Veziik/X95-TeleStock/CAM Job Files/v3 and earlier/jobs/SanityCheck/baseimage_t.png

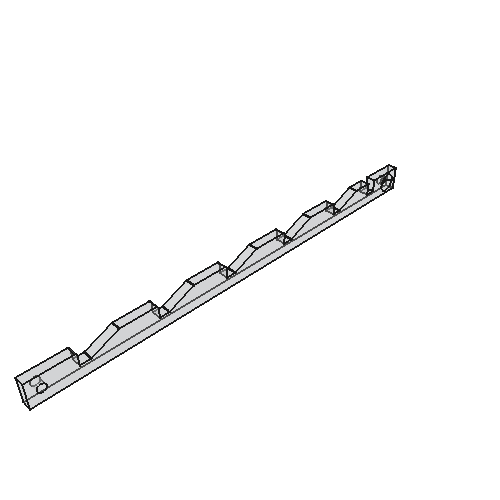
CAM Job Files/v3 and earlier/jobs/SanityCheck/baseimage_t.png
