Veziik/X95-TeleStock/CAM Job Files/v3 and earlier/jobs/SanityCheck/stockImage.png

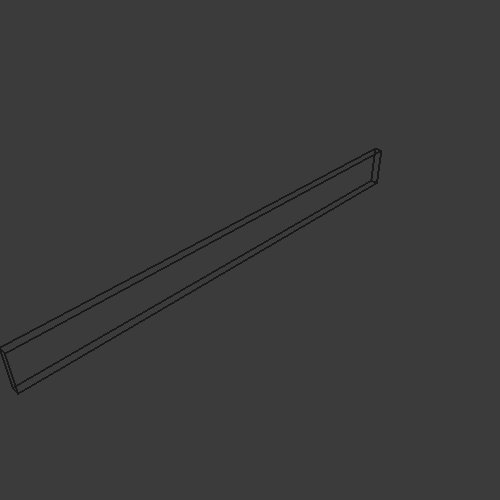
CAM Job Files/v3 and earlier/jobs/SanityCheck/stockImage.png
