Veziik/X95-TeleStock/Ender 5 Calibrated Files/ClevisPinSlotCover.stl

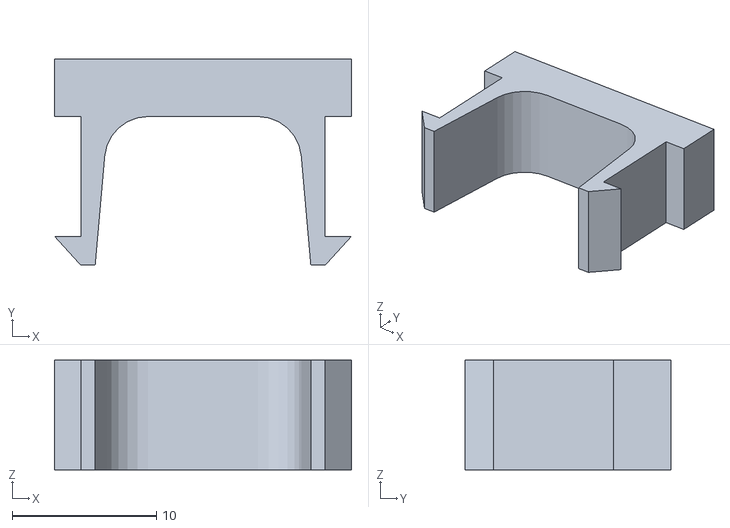
[picture p19: CAD file, 2026-01-05]
Ender 5 Calibrated Files/ClevisPinSlotCover.stl
20.6 x 14.3 x 7.60
