Veziik/X95-TeleStock/Modeling Files/Jigs and Spacers/step files/BarJig-BarSpacer-3-16inBar.step

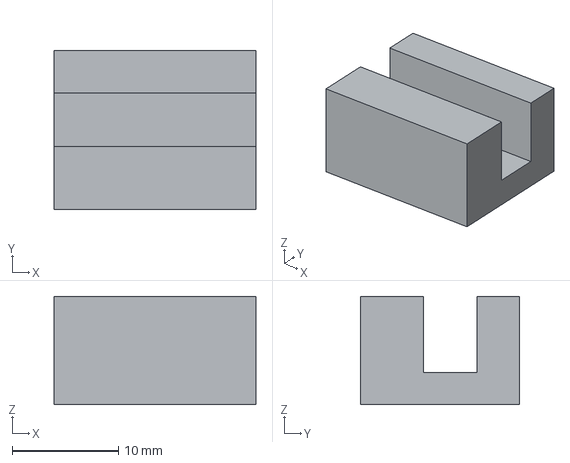
[picture p20: CAD file, 2026-07-19]
Modeling Files/Jigs and Spacers/step files/BarJig-BarSpacer-3-16inBar.step
19.0 x 15.0 x 10.2 mm
