Veziik/X95-TeleStock/X95TelescopingStock.FCStd

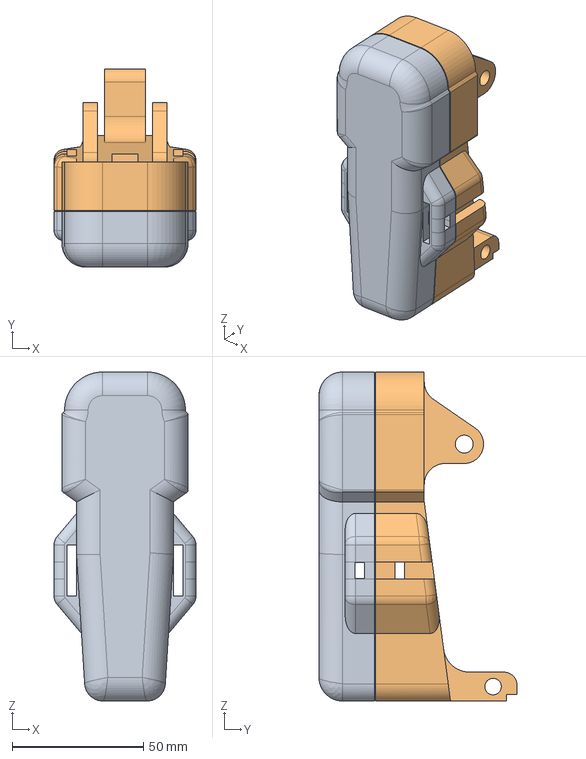
[picture p21: CAD file, 2024-03-01]
X95TelescopingStock.FCStd
54.2 x 75.6 x 125.5 mm
TelescopingPad
LockingBody
