Veziik/X95-TeleStock/Content Files/PaperworkSlotCover.step

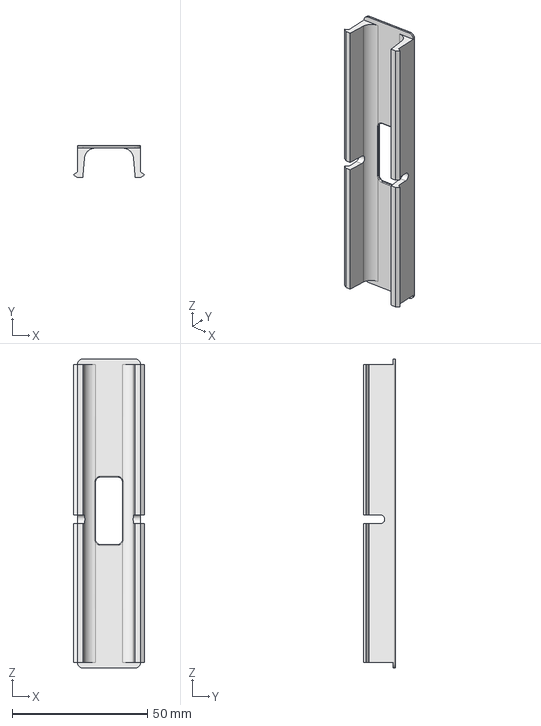
[picture p22: CAD file, 2026-07-30]
Content Files/PaperworkSlotCover.step
26.4 x 11.9 x 114.4 mm
