Veziik/X95-TeleStock/Content Files/WIP - Original Config - Updated Butt Texture - Rack UnEdited/TopPinArmPin.step

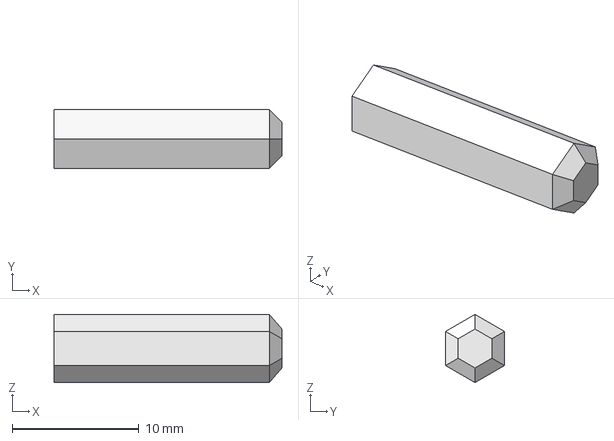
[picture p23: CAD file, 2026-07-19]
Content Files/WIP - Original Config - Updated Butt Texture - Rack UnEdited/TopPinArmPin.step
18.0 x 4.66 x 5.38 mm
