Veziik/X95-TeleStock/Content Files/WIP2 - RackProfileMovedRearwards/LockingPin.step

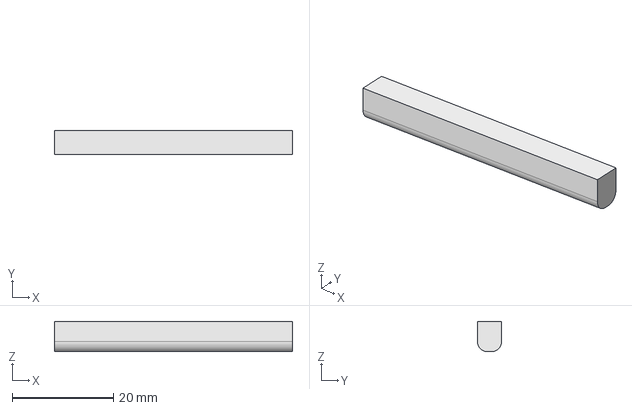
[picture p24: CAD file, 2026-07-19]
Content Files/WIP2 - RackProfileMovedRearwards/LockingPin.step
47.0 x 4.76 x 6.00 mm
