Veziik/X95-TeleStock/Ender 5 Calibrated Files/LockingBody.stl

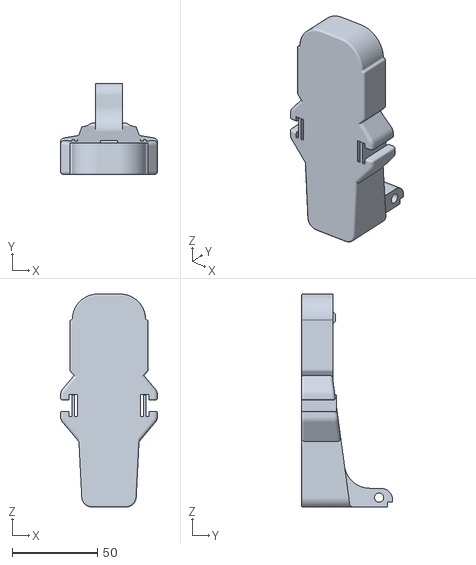
[picture p25: CAD file, 2026-01-05]
Ender 5 Calibrated Files/LockingBody.stl
56.9 x 53.6 x 125.0
