Veziik/X95-TeleStock/CAM Job Files/v3 and earlier/CAMAluminumLEftBar.FCStd

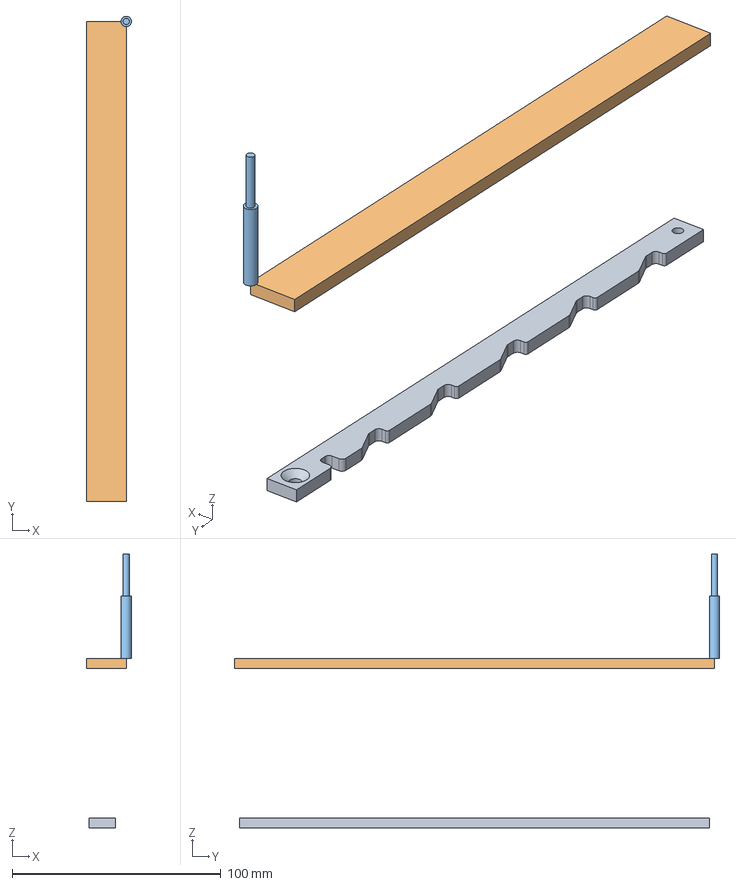
[picture p26: CAD file, 2026-07-19]
CAM Job Files/v3 and earlier/CAMAluminumLEftBar.FCStd
21.6 x 232.5 x 131.2 mm
Model-TelescopingBarArm-Left
Stock001
Endmill
