Veziik/X95-TeleStock/Content Files/TelescopingPad.step

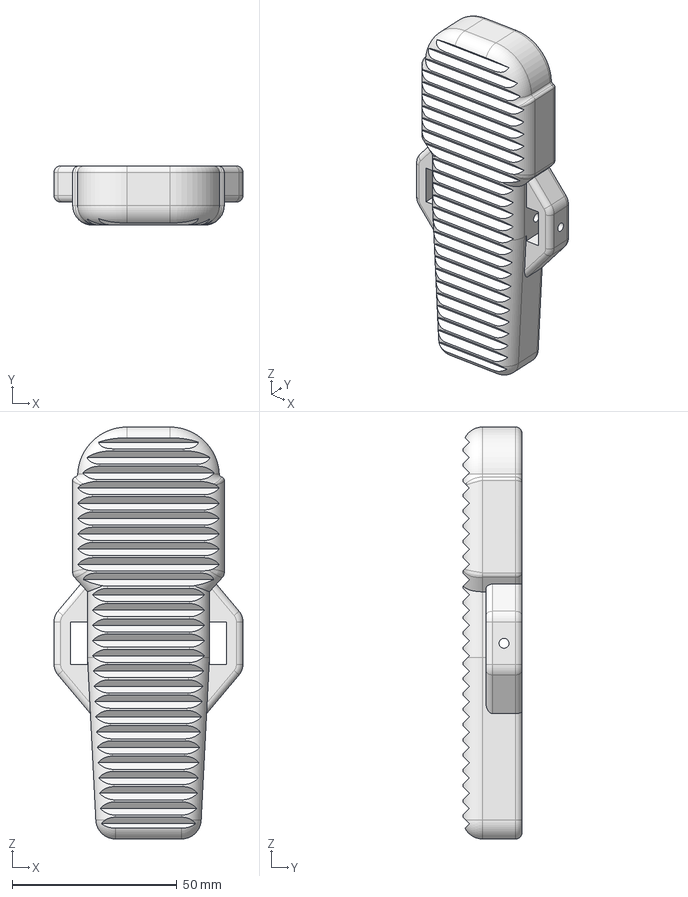
[picture p27: CAD file, 2026-07-23]
Content Files/TelescopingPad.step
57.3 x 18.0 x 125.0 mm
