Veziik/X95-TeleStock/Ender 5 Calibrated Files/PaperworkSlotLid.stl

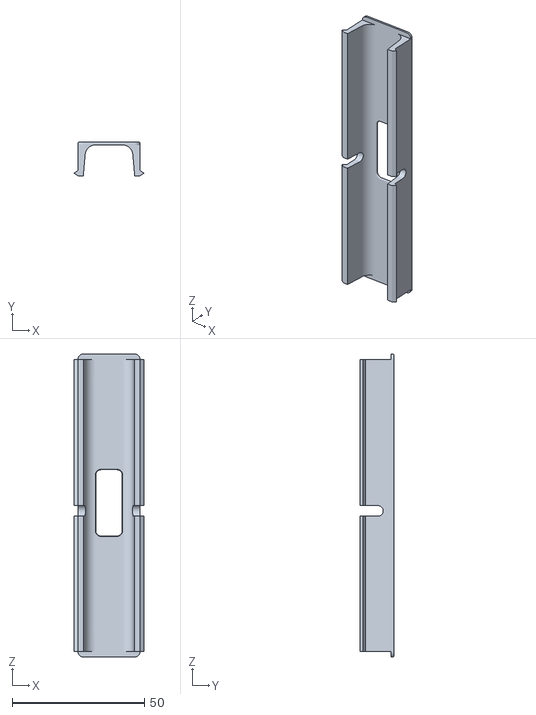
[picture p28: CAD file, 2026-01-05]
Ender 5 Calibrated Files/PaperworkSlotLid.stl
26.4 x 12.7 x 114.4
