Veziik/X95-TeleStock/Modeling Files/Jigs and Spacers/step files/BarSupport.step

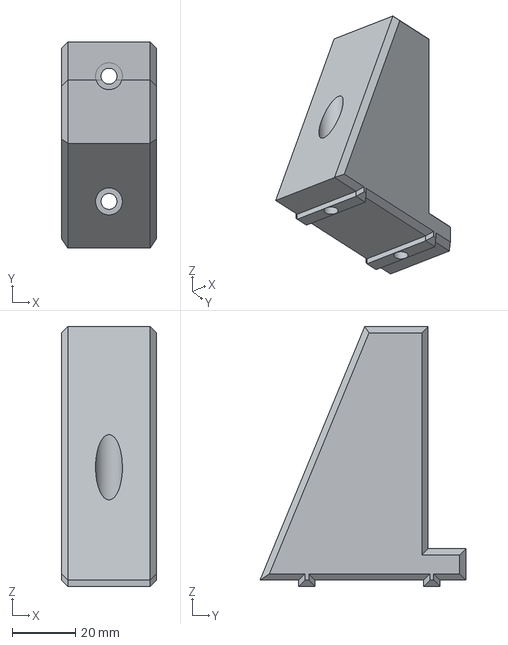
[picture p29: CAD file, 2026-07-19]
Modeling Files/Jigs and Spacers/step files/BarSupport.step
30.0 x 65.0 x 82.0 mm
