Veziik/X95-TeleStock/Modeling Files/X95SolidStock.FCStd

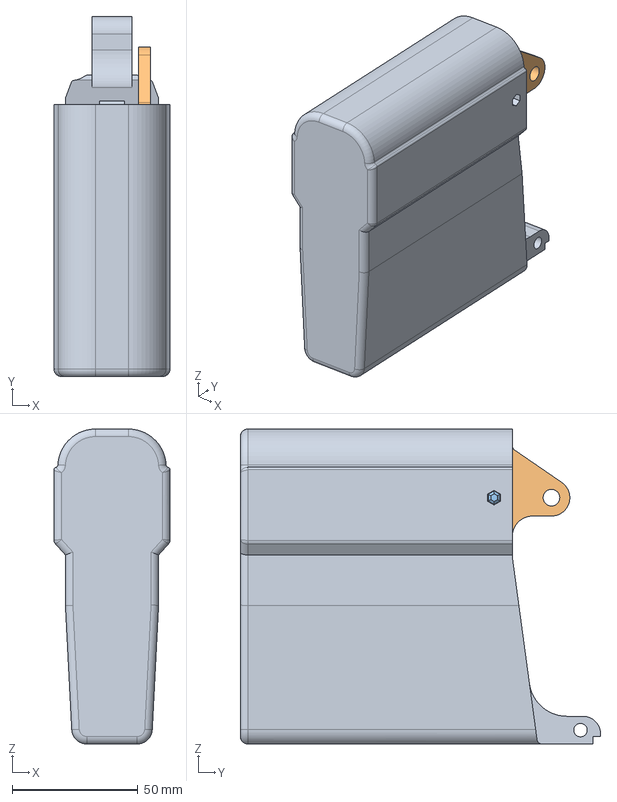
[picture p30: CAD file, 2026-07-19]
Modeling Files/X95SolidStock.FCStd
46.0 x 143.0 x 125.0 mm
SolidBody
MetalPinArm
TopPinArmPin
