Veziik/X95-TeleStock/CAM Job Files/v3 and earlier/CAMAluminumRightBar.FCStd

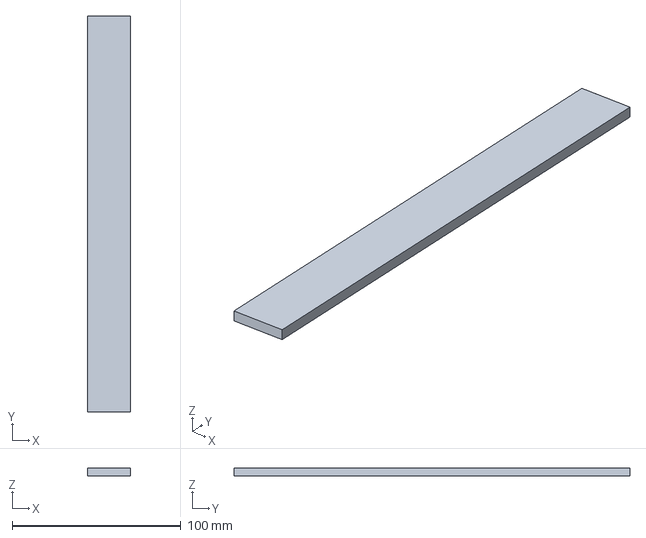
[picture p31: CAD file, 2026-07-19]
CAM Job Files/v3 and earlier/CAMAluminumRightBar.FCStd
25.4 x 235.0 x 4.76 mm
