Veziik/X95-TeleStock/Content Files/TopPinArmPin.step

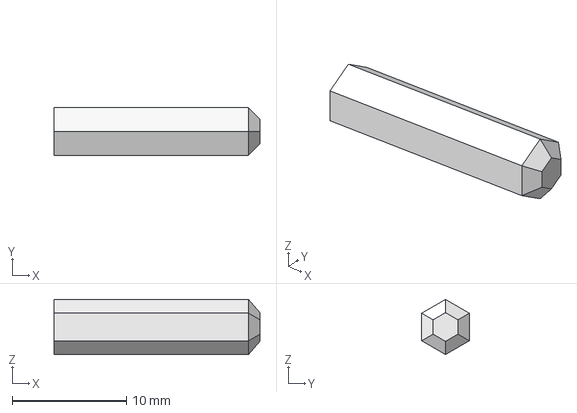
[picture p32: CAD file, 2026-07-23]
Content Files/TopPinArmPin.step
18.0 x 4.17 x 4.82 mm
