Veziik/X95-TeleStock/Ender 5 Calibrated Files/LockingBody for MetalPinArms.stl

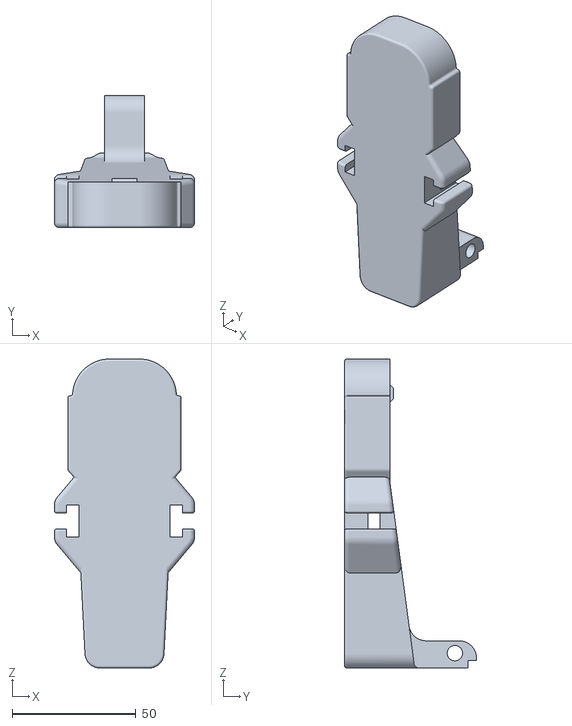
[picture p33: CAD file, 2024-08-24]
Ender 5 Calibrated Files/LockingBody for MetalPinArms.stl
56.7 x 53.4 x 125.0
