Veziik/X95-TeleStock/Modeling Files/Jigs and Spacers/step files/BarJig-BarSpacer-3-16inBarLong.step

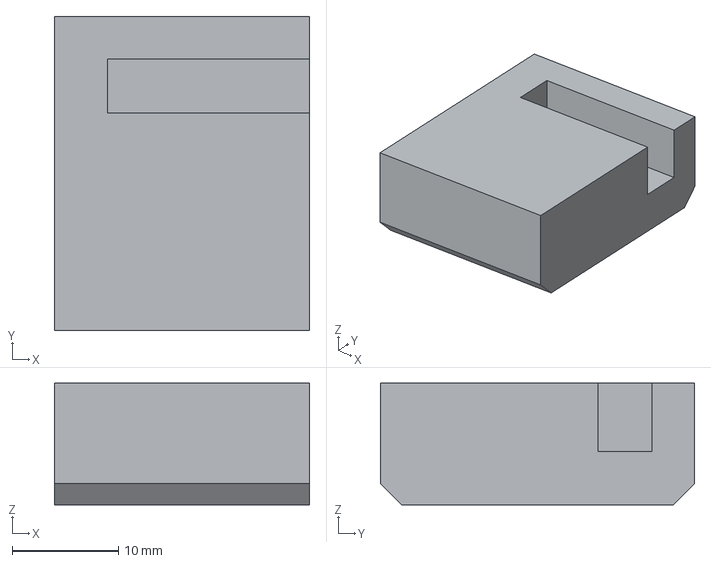
[picture p34: CAD file, 2026-07-19]
Modeling Files/Jigs and Spacers/step files/BarJig-BarSpacer-3-16inBarLong.step
24.0 x 29.5 x 11.4 mm
