Veziik/X95-TeleStock/Modeling Files/X95TelescopingStock-MetalPinoleArmsBetterModeling.FCStd

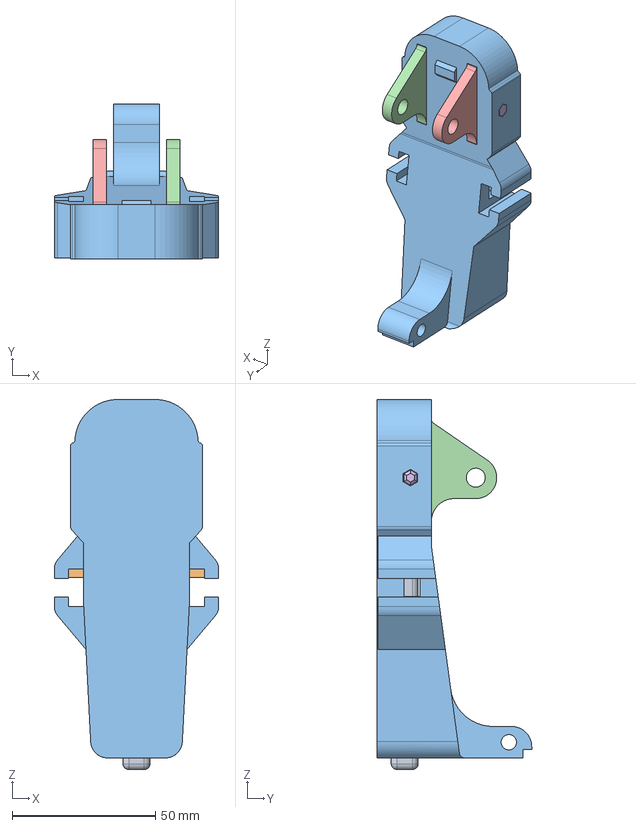
[picture p35: CAD file, 2026-07-19]
Modeling Files/X95TelescopingStock-MetalPinoleArmsBetterModeling.FCStd
57.3 x 53.9 x 129.0 mm
LockingButton
LockingPin
LockingBody
MetalPinArmMainBody
MetalPinArmMainBody (Mirror #3)
TopPinArmPin
