Veziik/X95-TeleStock/CAM Job Files/v3 and earlier/CAMAluminumLeftBar1-8Thick3-4wide.FCStd

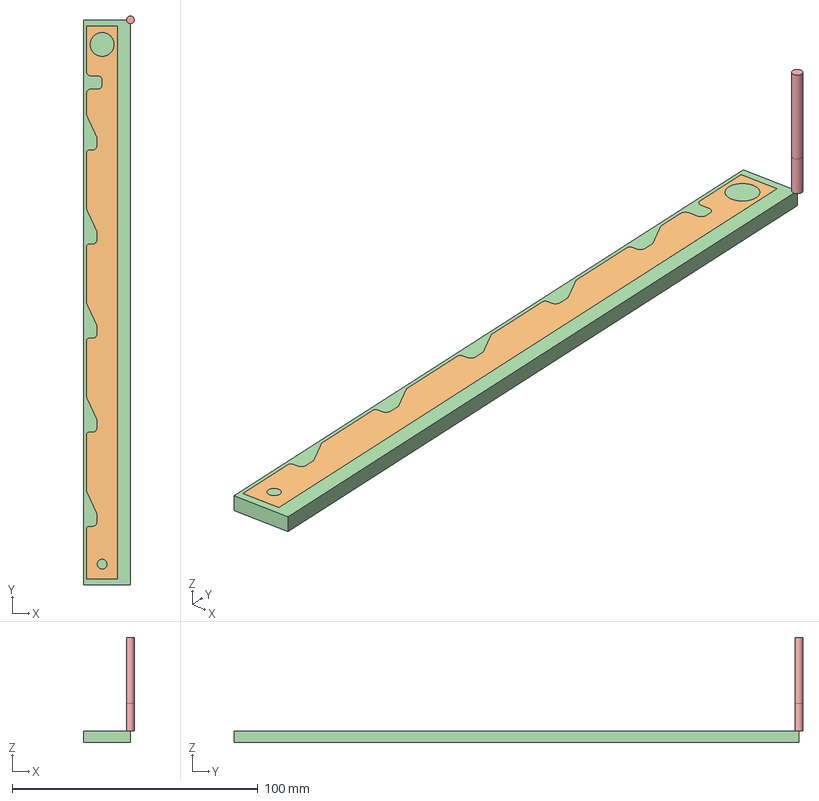
[picture p36: CAD file, 2026-07-19]
CAM Job Files/v3 and earlier/CAMAluminumLeftBar1-8Thick3-4wide.FCStd
20.6 x 231.6 x 42.9 mm
Model-TelescopingBarArm-Right
Model-TelescopingBarArm-Left
Stock001
Stock002
ALUMINUM | SpeTool Au3e 1/8 3FL | 5500rpm F100
ALUMINUM | SpeTool Au3e 1/8 3FL | 5500rpm F102
