Veziik/X95-TeleStock/Content Files/CountersinkFitting.step

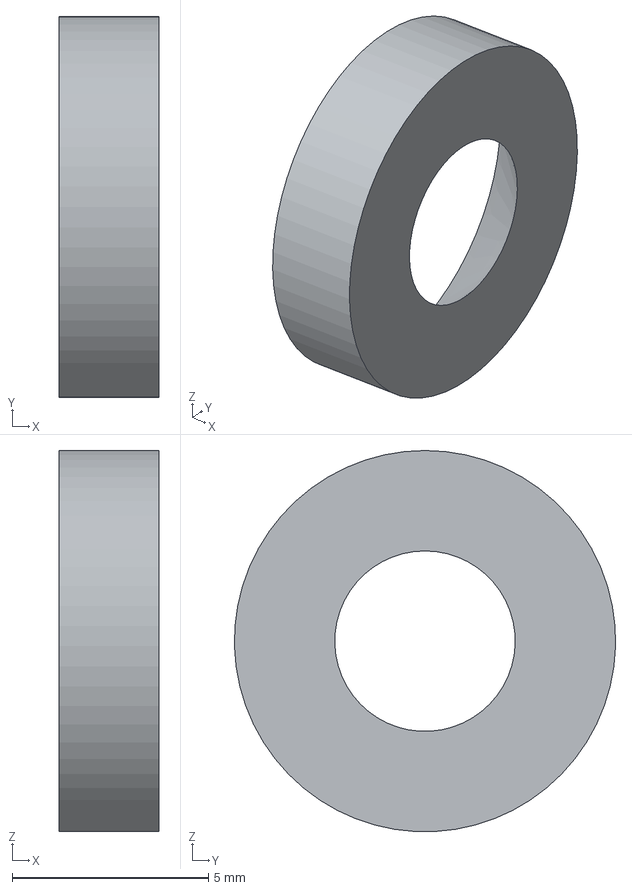
[picture p37: CAD file, 2026-07-23]
Content Files/CountersinkFitting.step
2.56 x 9.72 x 9.71 mm
