Veziik/X95-TeleStock/Ender 5 Calibrated Files/TopArm.dxf

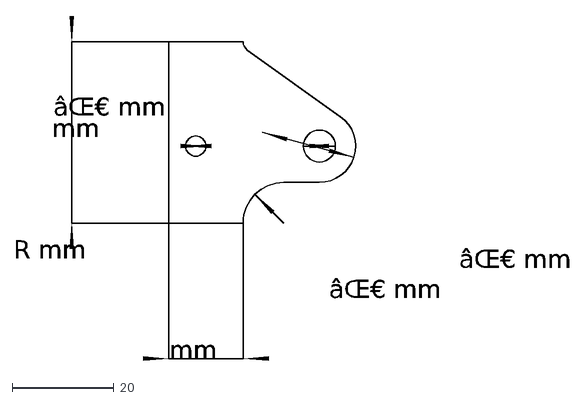
[picture p38: CAD file, 2024-08-24]
Ender 5 Calibrated Files/TopArm.dxf
mm
âŒ€ mm
R mm
