Veziik/X95-TeleStock/Modeling Files/Jigs and Spacers/step files/BarJig-BarSpacer.step

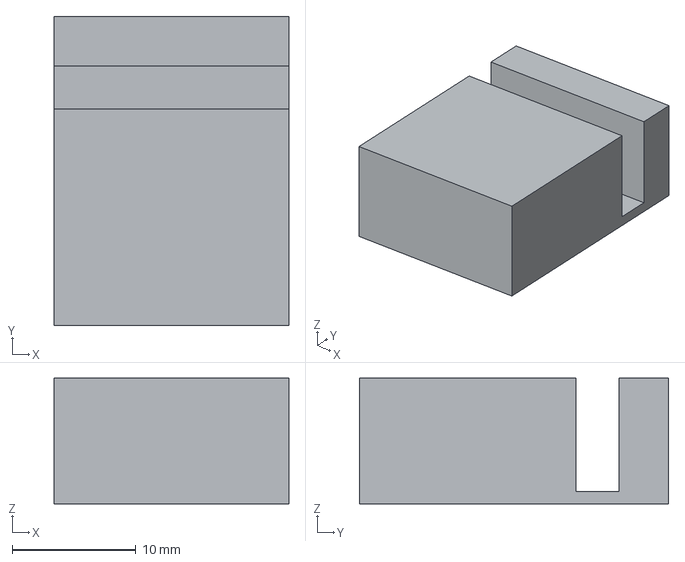
[picture p39: CAD file, 2026-07-19]
Modeling Files/Jigs and Spacers/step files/BarJig-BarSpacer.step
19.0 x 25.0 x 10.2 mm
