Veziik/X95-TeleStock/Content Files/LockingButton.step

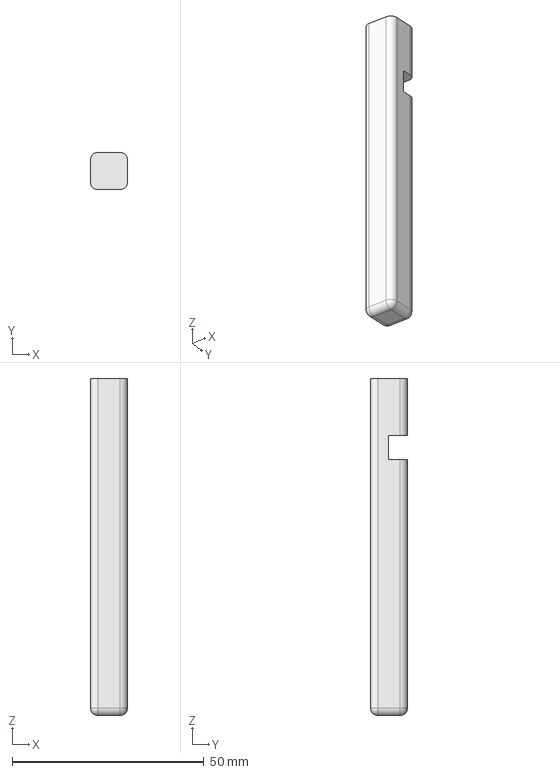
[picture p40: CAD file, 2026-07-23]
Content Files/LockingButton.step
9.70 x 9.70 x 87.9 mm
