Veziik/X95-TeleStock/Ender 5 Calibrated Files/Endcap-Left.stl

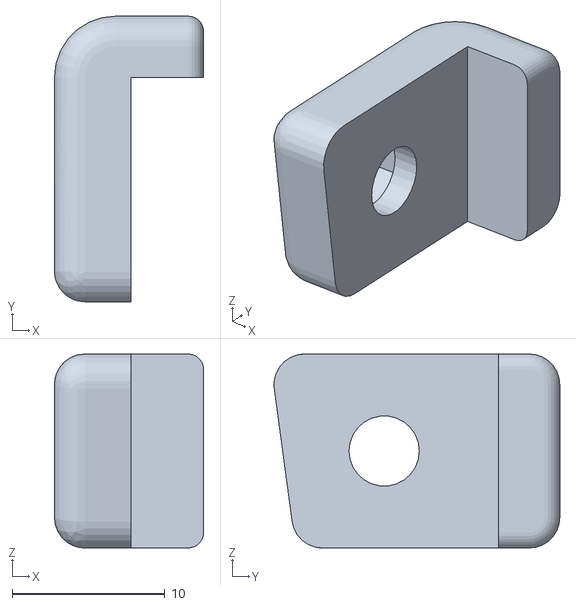
[picture p41: CAD file, 2024-05-17]
Ender 5 Calibrated Files/Endcap-Left.stl
9.76 x 18.7 x 12.7
