Veziik/X95-TeleStock/Modeling Files/Jigs and Spacers/step files/BarJig-BarSpacer-1-8-nolip.step

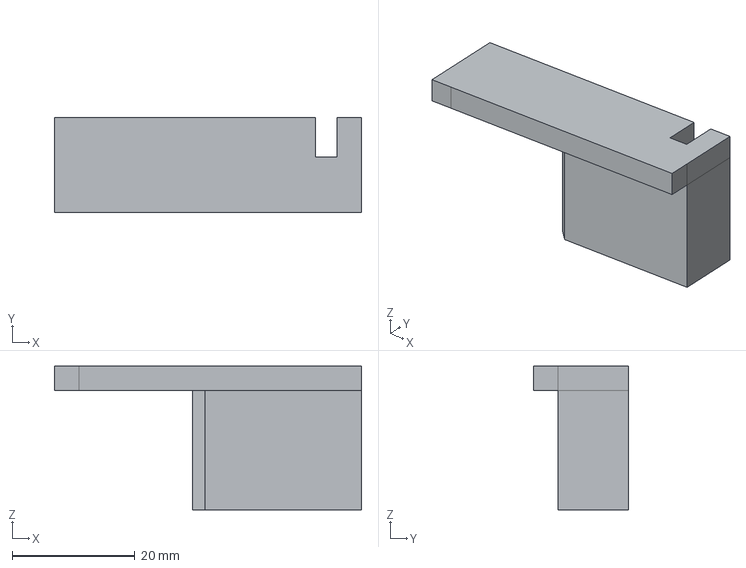
[picture p42: CAD file, 2026-07-19]
Modeling Files/Jigs and Spacers/step files/BarJig-BarSpacer-1-8-nolip.step
50.0 x 15.4 x 23.4 mm
