Veziik/X95-TeleStock/Ender 5 Calibrated Files/LockingPin.stl

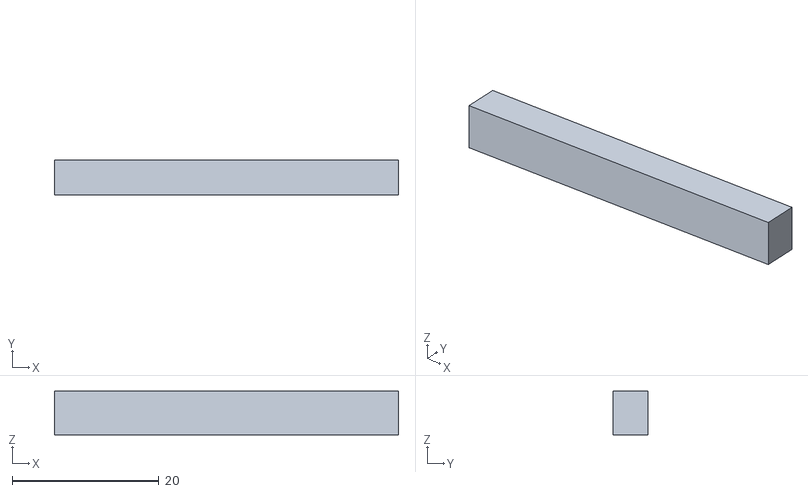
[picture p43: CAD file, 2024-05-17]
Ender 5 Calibrated Files/LockingPin.stl
46.9 x 4.76 x 6.00
