Veziik/X95-TeleStock/Modeling Files/Jigs and Spacers/step files/BarJig-BarSpacer-5mm-nolip.step

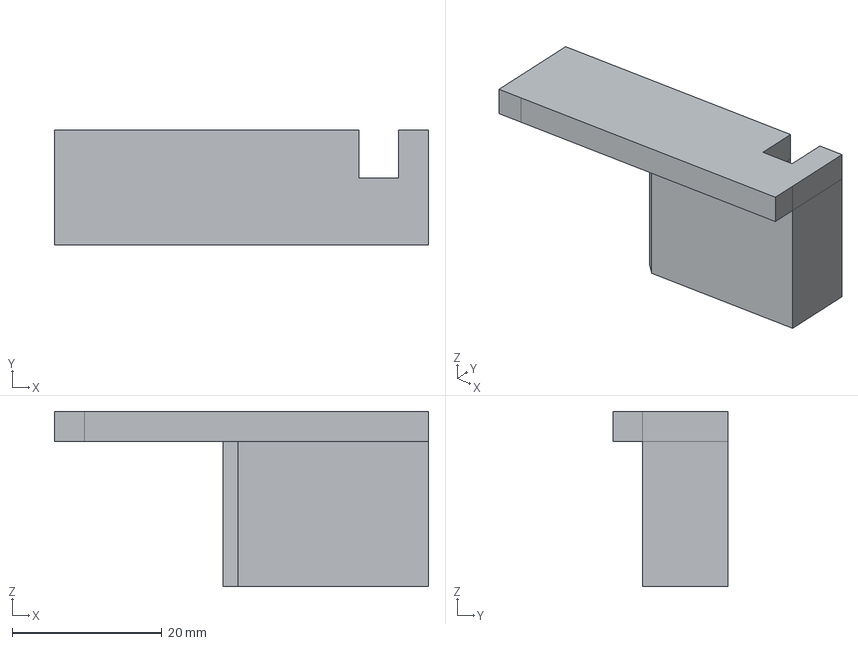
[picture p44: CAD file, 2026-07-19]
Modeling Files/Jigs and Spacers/step files/BarJig-BarSpacer-5mm-nolip.step
50.0 x 15.4 x 23.4 mm
