Veziik/X95-TeleStock/Ender 5 Calibrated Files/TelescopingBar-Left.stl

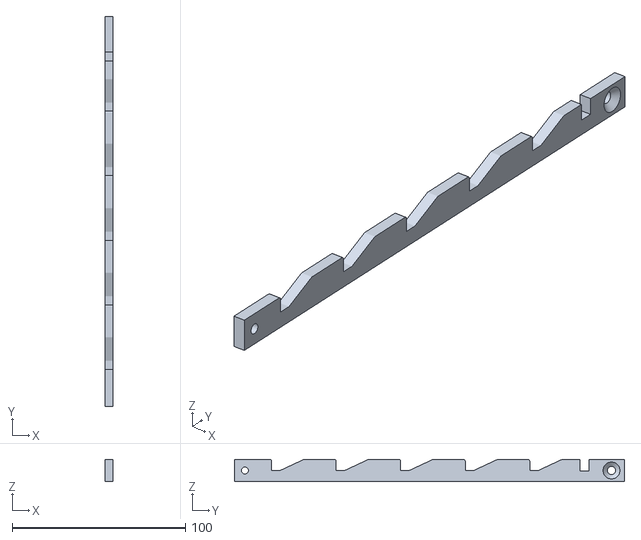
[picture p45: CAD file, 2024-05-17]
Ender 5 Calibrated Files/TelescopingBar-Left.stl
4.76 x 225.0 x 12.7
