Veziik/X95-TeleStock/Modeling Files/Jigs and Spacers/step files/BarSpacer-5mmx1in.step

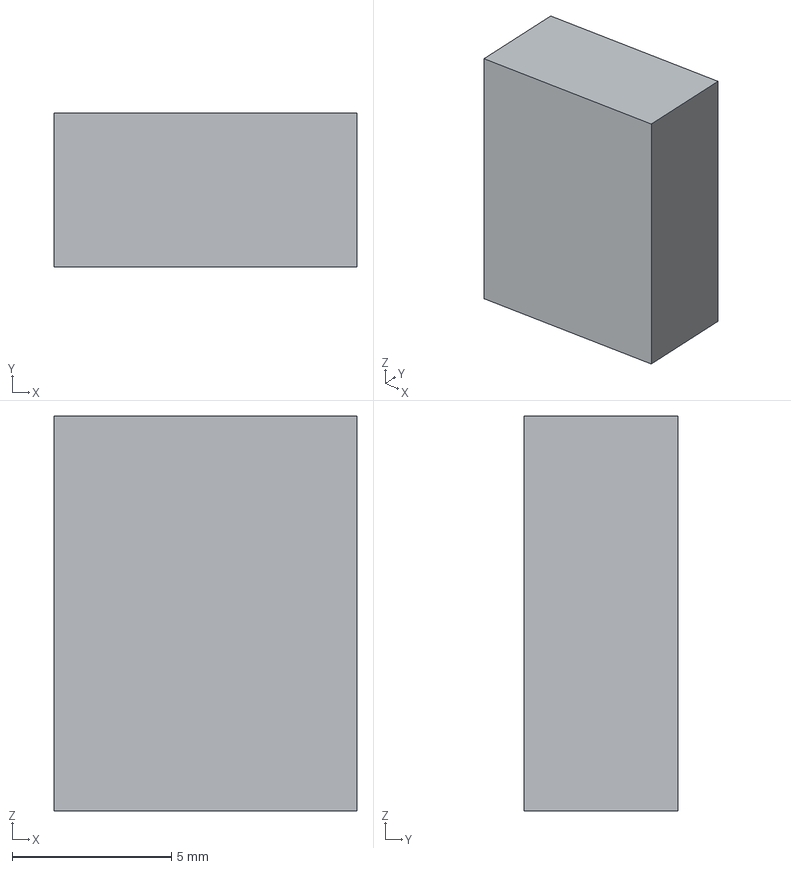
[picture p46: CAD file, 2026-07-19]
Modeling Files/Jigs and Spacers/step files/BarSpacer-5mmx1in.step
9.50 x 4.85 x 12.4 mm
