Veziik/X95-TeleStock/Modeling Files/Jigs and Spacers/step files/BarJig-BarSpacer3-16x1in-AllTheWayAround.step

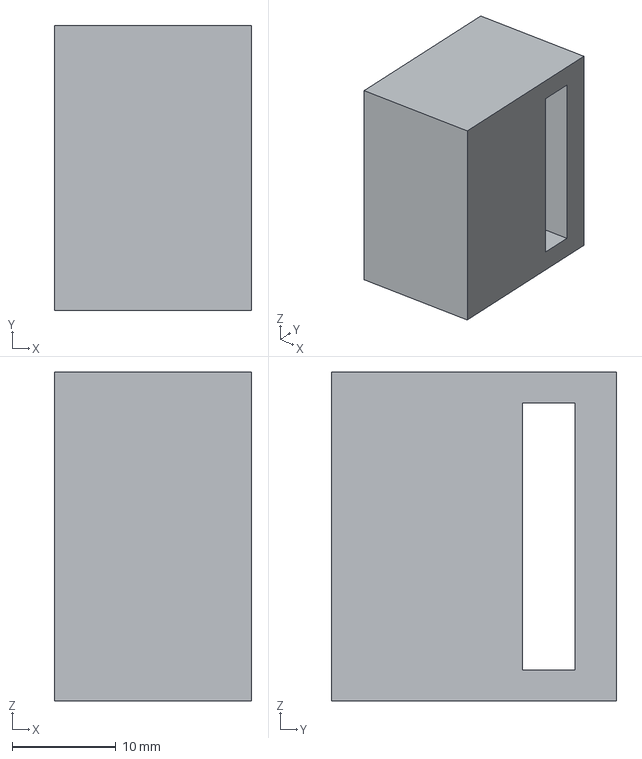
[picture p47: CAD file, 2026-07-19]
Modeling Files/Jigs and Spacers/step files/BarJig-BarSpacer3-16x1in-AllTheWayAround.step
19.0 x 27.5 x 31.7 mm
