Veziik/X95-TeleStock/Ender 5 Calibrated Files/TelescopingBar.dxf

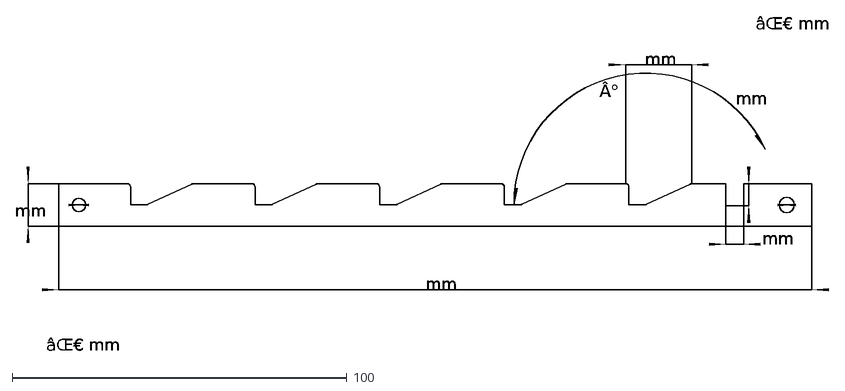
[picture p48: CAD file, 2024-05-17]
Ender 5 Calibrated Files/TelescopingBar.dxf
mm
âŒ€ mm
Â°
